jcksnvllxr80/raspi_pico_christmas_tree/pcb/images/raspi_pico_christmas_tree_angle_3d.jpg

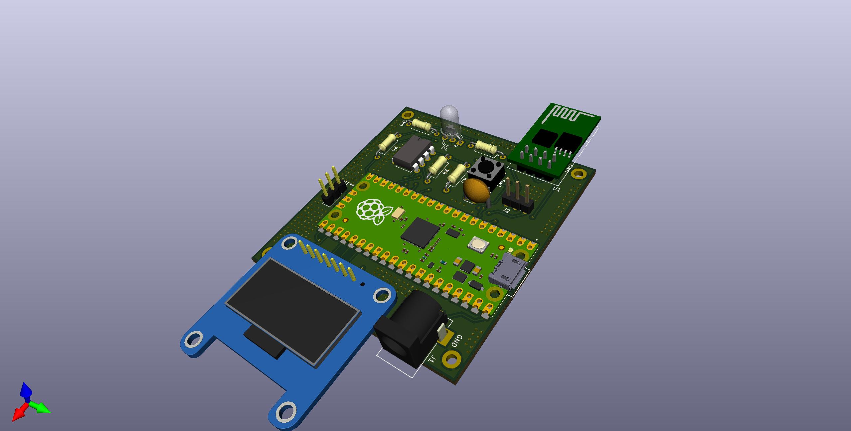
pcb/images/raspi_pico_christmas_tree_angle_3d.jpg
