jcksnvllxr80/raspi_pico_christmas_tree/eeprom/EEPROM_24LC512.py

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
# For 4KB EEPROMS.
# EEPROMS from different manufacturers have different Page and Bytes per page numbers. Get these numbers from your EEPROM manufacturer's datasheet and change the values here.

import time


class EEPROM_24LC512(object):

    def __init__(self, i2c, i2c_addr, pages=128, bpp=128):
        self.i2c = i2c
        self.i2c_addr = i2c_addr
        self.pages = pages
        self.bpp = bpp  # bytes per page

    def capacity(self):
        """Storage capacity in bytes"""
        return self.pages * self.bpp

    def read(self, addr, nbytes):
        """Read one or more bytes from the EEPROM starting from a specific address"""
        return self.i2c.readfrom_mem(self.i2c_addr, addr, nbytes, addrsize=16)

    def write(self, addr, buf):
        """Write one or more bytes to the EEPROM starting from a specific address"""
        offset = addr % self.bpp
        partial = 0
        # partial page write
        if offset > 0:
            partial = self.bpp - offset
            self.i2c.writeto_mem(self.i2c_addr, addr,
                                 buf[0:partial], addrsize=16)
            time.sleep_ms(5)
            addr += partial
        # full page write
        for i in range(partial, len(buf), self.bpp):
            self.i2c.writeto_mem(self.i2c_addr, addr+i -
                                 partial, buf[i:i+self.bpp], addrsize=16)
            time.sleep_ms(5)

    def wipe(self):
        buf = b'\xff' * 128
        for i in range(128):
            self.write(i*512, buf)
