jcksnvllxr80/raspi_pico_christmas_tree/examples/raspberry_pi_logo/main.py

###############################################################
# SSD1306 OLED Display I2C Tests with the Raspberry Pi Pico
# with MicroPython on the Raspberry Pi 4
#
# by Joshua Hrisko, Maker Portal LLC (c) 2021
#
#
# Based on the Pico Micropython repository at:
# https://github.com/raspberrypi/pico-micropython-examples/tree/master/i2c/1306oled
###############################################################
#
#
from machine import Pin, I2C
from ssd1306 import SSD1306_I2C
import framebuf
import sys
import imgfile

pix_res_x = 128  # SSD1306 horizontal resolution
pix_res_y = 64   # SSD1306 vertical resolution

# start I2C on I2C1 (GPIO 26/27)
i2c_dev = I2C(1, scl=Pin(27), sda=Pin(26), freq=200000)
i2c_addr = [hex(ii) for ii in i2c_dev.scan()]  # get I2C address in hex format
if i2c_addr == []:
    print('No I2C Display Found')
    sys.exit()  # exit routine if no dev found
else:
    print("I2C Address      : {}".format(i2c_addr[0]))  # I2C device address
    print("I2C Configuration: {}".format(i2c_dev))  # print I2C params


oled = SSD1306_I2C(pix_res_x, pix_res_y, i2c_dev)  # oled controller

# Raspberry Pi logo as 32x32 bytearray
buffer = bytearray(b"\x00\x00\x00\x00\x00\x00\x00\x00\x00\x00\x00\x00\x00|?\x00\x01\x86@\x80\x01\x01\x80\x80\x01\x11\x88\x80\x01\x05\xa0\x80\x00\x83\xc1\x00\x00C\xe3\x00\x00~\xfc\x00\x00L'\x00\x00\x9c\x11\x00\x00\xbf\xfd\x00\x00\xe1\x87\x00\x01\xc1\x83\x80\x02A\x82@\x02A\x82@\x02\xc1\xc2@\x02\xf6>\xc0\x01\xfc=\x80\x01\x18\x18\x80\x01\x88\x10\x80\x00\x8c!\x00\x00\x87\xf1\x00\x00\x7f\xf6\x00\x008\x1c\x00\x00\x0c \x00\x00\x03\xc0\x00\x00\x00\x00\x00\x00\x00\x00\x00\x00\x00\x00\x00")

# Load the raspberry pi logo into the framebuffer (the image is 32x32)
fb = framebuf.FrameBuffer(buffer, 32, 32, framebuf.MONO_HLSB)

# Clear the oled display in case it has junk on it.
oled.fill(0)

# Blit the image from the framebuffer to the oled display
oled.blit(fb, 96, 0)

# Add some text
oled.text("Raspberry Pi", 5, 5)
oled.text("Pico", 5, 15)

# Finally update the oled display so the image & text is displayed
oled.show()
